Muten-Roshi-Sama/PCB_Design-Doorbuzzer/ReportImages/NE555_mono_simul.png

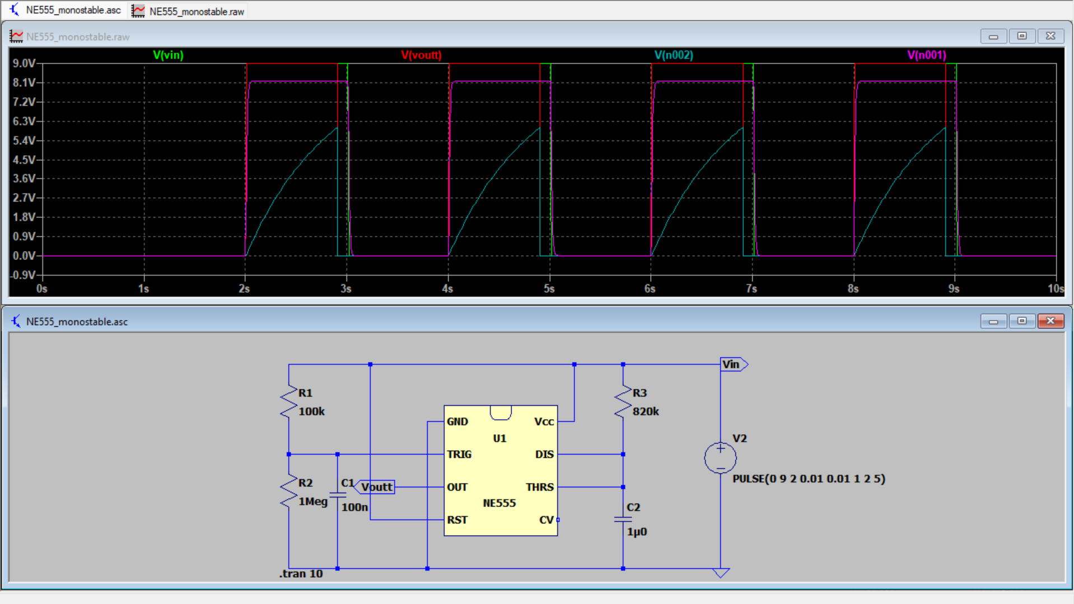
ReportImages/NE555_mono_simul.png
