Muten-Roshi-Sama/PCB_Design-Doorbuzzer/LTSPICE_Simulations/Draft1.asc

5.95Giga: res; 5.95G
C1: cap; 6n8
V3: voltage; SINE(0 9 2 0 0 0 2); AC 9
Named nets: 0, N1
.ac dec 1000 1 10000
