Muten-Roshi-Sama/PCB_Design-Doorbuzzer/LTSPICE_Simulations/Full_circuit.asc

C1: cap; 100n
C2: cap; 1µ0
C3: polcap; 100µ; V=10 Irms=0 Rser=0.1 Lser=0 mfg="AVX" pn="TPSD107M010R0100" type="Tantalum"
C4: polcap; 100µ; V=10 Irms=0 Rser=0.1 Lser=0
C5: cap; 6n8; V=6.3 Irms=173m Rser=1.00156 Lser=0
Q1: npn
R1: res; 100k
R2: res; 1Meg
R3: res; 820k
R4: res; 68.1K; tol=1 pwr=0.1
R5: res; 100k; tol=1 pwr=0.1
R6: res; 100K; tol=1 pwr=0.1
R7: res; 49.9K; tol=1 pwr=0.1
R8: res; 1k; tol=1 pwr=0.1
R9: res; 47.5K; tol=1 pwr=0.1
U1: NE555
U4: LT1006
V3: voltage; PULSE(0 9 2.2 0.1 0.1 3 5 5)
Named nets: Vin, 0, Speaker, VR55, VR77, VR66
.tran 10
