Muten-Roshi-Sama/PCB_Design-Doorbuzzer/LTSPICE_Simulations/NE555_monostable.asc

C1: cap; 100n
C2: cap; 1µ0
R1: res; 100k
R2: res; 1Meg
R3: res; 820k
U1: NE555
V2: voltage; PULSE(0 9 2 0.05 0.05 2 6 5)
Named nets: 0, Vin, Voutt
.tran 10
